miguelboing/electronics_project_1/main/devices/servo_motor/servo_motor.c

#include "servo_motor.h"
#include "iot_servo.h"
#include "driver/gpio.h"

#define sMOTOR GPIO_NUM_19 /* D19 */


void servo_motor_init(void) {

    servo_config_t servo_cfg = {
            .max_angle = 180,
            .min_width_us = 500,
            .max_width_us = 2500,
            .freq = 50,
            .timer_number = LEDC_TIMER_0,
            .channels = {
                    .servo_pin = {
                            sMOTOR,
                    },
                    .ch = {
                            LEDC_CHANNEL_5,
                    },
            },
            .channel_number = 1,
    };

    if (iot_servo_init(LEDC_LOW_SPEED_MODE, &servo_cfg)== ESP_OK)
    {
        printf("Servo motor initialized successfully!");
    }

}

void servo_motor_open(void)
{
    iot_servo_write_angle(LEDC_LOW_SPEED_MODE, 5, 180.0f);
}

void servo_motor_close(void)
{
    iot_servo_write_angle(LEDC_LOW_SPEED_MODE, 5, 0.0f);
}
