miguelboing/electronics_project_1/main/devices/servo_motor/servo_motor.h

/*
 * servo_motor.h
 *
 *  Created on: 18 de mai de 2022
 *
 */

#ifndef SERVO_MOTOR_H_
#define SERVO_MOTOR_H_

void servo_motor_init(void);

void servo_motor_open(void);

void servo_motor_close(void);

#endif /* SERVO_MOTOR_H_ */
