miguelboing/electronics_project_1/main/devices/proximity_sensor/proximity_sensor.h

/*
 * proximity_sensor.h
 *
 *  Created on: 18 de mai de 2022
 *
 */

#ifndef PROXIMITY_SENSOR_H_
#define PROXIMITY_SENSOR_H_


void proximity_sensor_init(void);

int proximity_sensor_get_presence(void);

#endif /* PROXIMITY_SENSOR_H_ */
